db00lean/Capstone/Hardware/LTSpice Simulations/Results/Inductor-SwitchingFrequency/Inductance-10uF/700KHz.png

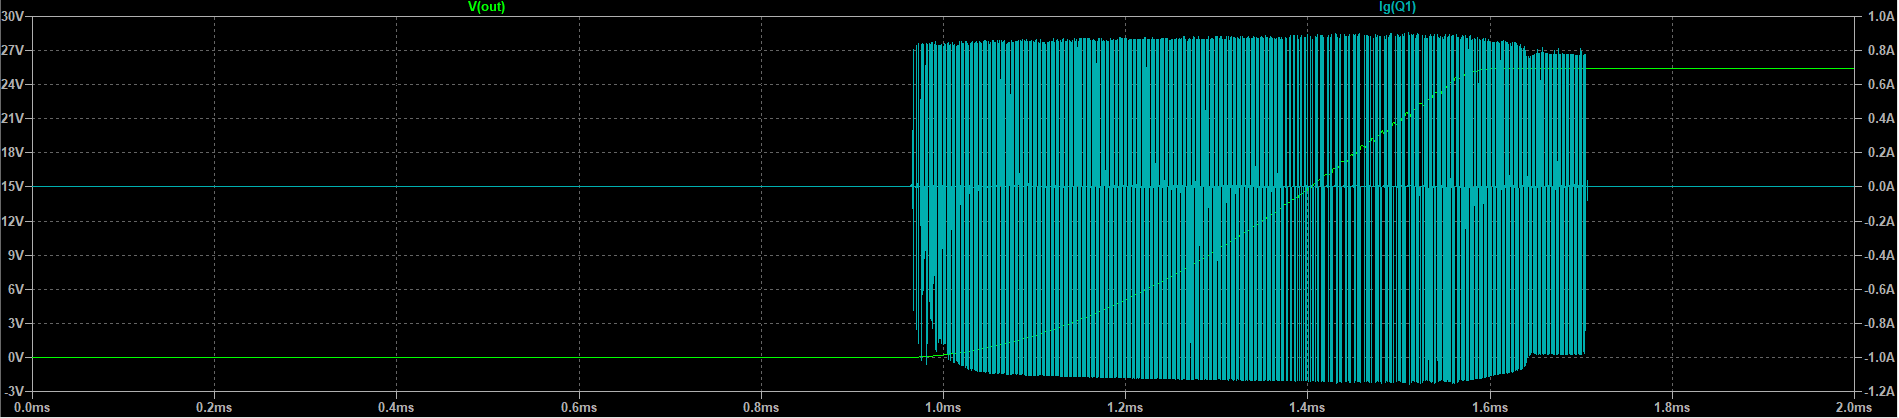
Hardware/LTSpice Simulations/Results/Inductor-SwitchingFrequency/Inductance-10uF/700KHz.png
