db00lean/Capstone/Hardware/LTSpice Simulations/LT3790_Inductor-SwitchingFrequency.asc

C1: cap; 33n
C2: cap; 10n
C3: cap; 470n
C4: cap; 4.7µ
C5: cap; .1µ
C6: cap; .1µ
C7: cap; .1µ
C8: cap; 4.7µ; x2; V=50 Irms=0 Rser=0.005 Lser=0
C9: polcap; 220µ; V=35 Irms=760m Rser=0.09 Lser=0 mfg="Panasonic" pn="ECA1VFQ221" type="Al electrolytic"
C10: cap; 1µ; V=100 Rser=.025
C11: cap; 47µ; V=63 Rser=.025
D1: schottky; BAT46WJ
D2: schottky; BAT46WJ
L1: ind; 10µ; Rser=20m Rpar=5K
Q1: nmos; RJK0651DPB
Q2: nmos; RJK0651DPB
Q3: nmos; Si4840DY
Q4: nmos; Si4840DY
R1: res; 3m
R2: res; 866k
R3: res; 895k
R4: res; 51
R5: res; 1Meg
R6: res; 57.6
R7: res; 147K
R8: res; 4m
R9: res; 245K
R10: res; 5K
R11: res; 9m
R12: res; 200K
R13: res; 100K
R14: res; 100K
R15: res; 5.1K
Rload: res; 5k
U1: LT3790
V1: voltage; 5V
Named nets: 0, IN, OUT
.tran 10m startup
Note:
  If the simulation model is not found please update with the "Sync Release" command from the "Tools" menu.
  It remains the customer's responsibility to verify proper and reliable operation in the actual application.
  Component substitution and printed circuit board layout may significantly affect circuit performance or reliability.
  Contact your local sales representative for assistance. This circuit is distributed to customers only for use with LTC parts.
  Copyright © 2015 Linear Technology Inc. All rights reserved.
LT3790 - 60V Synchronous 4-Switch Buck-Boost Controller
120W Buck-Boost Voltage Regulator
Input: 12V to 57V     Output: 24V @ 5A, Fsw = 200kHz
