db00lean/Capstone/Hardware/LTSpice Simulations/LT3790_rev_A01.asc

C1: cap; .1µ
C2: cap; .1µ
C7: cap; 470n
C8: cap; .1µ
C11: cap; 47µ; V=63 Rser=.025
Cc: cap; 10n
Cin: cap; 1µ; V=100 Rser=.025
Cout2: polcap; 220µ; V=35 Irms=760m Rser=0.09 Lser=0 mfg="Panasonic" pn="ECA1VFQ221" type="Al electrolytic"
Cout: cap; 4.7µ; x2; V=50 Irms=0 Rser=0.005 Lser=0
Css: cap; 33n
Cvcc: cap; 4.7µ
D1: schottky; BAT46WJ
D2: schottky; BAT46WJ
L1: ind; 10µ; Rser=20m Rpar=5K
M1: nmos; RJK0651DPB
M2: nmos; RJK0651DPB
M3: nmos; Si4840DY
M4: nmos; Si4840DY
R1: res; 499K
R2: res; 56.2K
R3: res; 499K
R4: res; 27.4K
R5: res; 73.2K
R6: res; 3.83K
R7: res; 50
R8: res; 147K
R9: res; 100K
R10: res; 200K
Rc: res; 5.1K
Rfault: res; 100K
Rin: res; 3m
Rload: res; 4.8
Rout: res; 8m
Rsense: res; 4m
U1: LT3790
Vin: voltage; 5
Named nets: 0, IN, OUT
.tran 2m startup
Note:
  If the simulation model is not found please update with the "Sync Release" command from the "Tools" menu.
  It remains the customer's responsibility to verify proper and reliable operation in the actual application.
  Component substitution and printed circuit board layout may significantly affect circuit performance or reliability.
  Contact your local sales representative for assistance. This circuit is distributed to customers only for use with LTC parts.
  Copyright © 2015 Linear Technology Inc. All rights reserved.
LT3790 - 60V Synchronous 4-Switch Buck-Boost Controller
120W Buck-Boost Voltage Regulator
Input: 12V to 57V     Output: 24V @ 5A, Fsw = 200kHz
Does not include D5 and D6 (shown in single-IC application circuit and not in dual-IC circuit)
Missing diodes D3, D4
